jamiejcole/zenith/Code/MK2.5/test/interrupttest/interrupttest.ino

#include <Arduino.h>
#include <Wire.h>
#include "Adafruit_MCP23017.h"
#include "Rotary.h"
#include "RotaryEncOverMCP.h"

#define INTERRUPT_FUNC_ATTRIB IRAM_ATTR

/* Our I2C MCP23017 GPIO expanders */
Adafruit_MCP23017 mcp;

//Array of pointers of all MCPs if there is more than one
Adafruit_MCP23017* allMCPs[] = { &mcp };
constexpr int numMCPs = (int)(sizeof(allMCPs) / sizeof(*allMCPs));

/* the INT pin of the MCP can only be connected to
 * an interrupt capable pin on the Arduino, either
 * D3 or D2.
 * */
int arduinoIntPin = 12;

/* variable to indicate that an interrupt has occured */
volatile boolean awakenByInterrupt = false;

/* function prototypes */
void intCallBack();
void cleanInterrupts();
void handleInterrupt();
void RotaryEncoderChanged(bool clockwise, int id);

/* Array of all rotary encoders and their pins */
RotaryEncOverMCP rotaryEncoders[] = {
    // outputA,B on GPB7,GPB6, register with callback and ID=1 (GPB0=7 .. GPB7=15)
    RotaryEncOverMCP(&mcp, 6, 7, &RotaryEncoderChanged, 1),
    // outputA,B on GPA0,GPA1, register with callback and ID=2
    RotaryEncOverMCP(&mcp, 4, 5, &RotaryEncoderChanged, 2)
};
constexpr int numEncoders = (int)(sizeof(rotaryEncoders) / sizeof(*rotaryEncoders));

void RotaryEncoderChanged(bool clockwise, int id) {
    Serial.println("Encoder " + String(id) + ": "
            + (clockwise ? String("clockwise") : String("counter-clock-wise")));
}

void setup(){

    Serial.begin(115200);
    Serial.println("MCP23007 Interrupt Test");

    pinMode(arduinoIntPin,INPUT);

    mcp.begin();      // use default address 0
    Wire.setClock(400000);
    mcp.readINTCAPAB(); //read this so that the interrupt is cleared

    //initialize all rotary encoders

    //Setup interrupts, OR INTA, INTB together on both ports.
    //thus we will receive an interrupt if something happened on
    //port A or B with only a single INT connection.
    mcp.setupInterrupts(true,false,LOW);

    //Initialize input encoders (pin mode, interrupt)
    for(int i=0; i < numEncoders; i++) {
        rotaryEncoders[i].init();
    }

    attachInterrupt(digitalPinToInterrupt(arduinoIntPin), intCallBack, FALLING);
}

// The int handler will just signal that the int has happened
// we will do the work from the main loop.
void INTERRUPT_FUNC_ATTRIB intCallBack() {
    awakenByInterrupt=true;
}

void checkInterrupt() {
    if(awakenByInterrupt) {
        // disable interrupts while handling them.
        Serial.println("interrupt awoken! detaching interrupt...");
        detachInterrupt(digitalPinToInterrupt(arduinoIntPin));
        handleInterrupt();
        Serial.println("attaching interrupts!");
        mcp.readINTCAPAB();
        attachInterrupt(digitalPinToInterrupt(arduinoIntPin),intCallBack,FALLING);
    }
}

void handleInterrupt(){
    //Read the entire state when the interrupt occurred

    //An interrupt occurred on some MCP object.
    //since all of them are ORed together, we don't
    //know exactly which one has fired.
    //just read all of them, pre-emptively.
    Serial.println("handling interrupt!");
    for(int j = 0; j < numMCPs; j++) {
        uint16_t gpioAB = allMCPs[j]->readINTCAPAB();
        // we need to read GPIOAB to clear the interrupt actually.
        volatile uint16_t dummy = allMCPs[j]->readGPIOAB();
        for (int i=0; i < numEncoders; i++) {
            //only feed this in the encoder if this
            //is coming from the correct MCP
            if(rotaryEncoders[i].getMCP() == allMCPs[j])
                rotaryEncoders[i].feedInput(gpioAB);
                Serial.print("feeding encoder input ");
                Serial.println(i);
        }
    }

    cleanInterrupts();
}

// handy for interrupts triggered by buttons
// normally signal a few due to bouncing issues
void cleanInterrupts(){
#ifdef __AVR__
    EIFR=0x01;
#endif
    awakenByInterrupt=false;
    Serial.println("cleaning interrupts!");
}

void loop() {
    //Check if an interrupt has occurred and act on it
    checkInterrupt();
    delay(1);
}
