jamiejcole/zenith/Code/MK2.5/test/Bounce2mcp.h

/*
  The MIT License (MIT)

  Copyright (c) 2013 thomasfredericks

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
  THE SOFTWARE IS PROVIDED "AS IS", WITHOUT WARRANTY OF ANY KIND, EXPRESS OR
  IMPLIED, INCLUDING BUT NOT LIMITED TO THE WARRANTIES OF MERCHANTABILITY, FITNESS
  FOR A PARTICULAR PURPOSE AND NONINFRINGEMENT. IN NO EVENT SHALL THE AUTHORS OR
  COPYRIGHT HOLDERS BE LIABLE FOR ANY CLAIM, DAMAGES OR OTHER LIABILITY, WHETHER
  IN AN ACTION OF CONTRACT, TORT OR OTHERWISE, ARISING FROM, OUT OF OR IN
  CONNECTION WITH THE SOFTWARE OR THE USE OR OTHER DEALINGS IN THE SOFTWARE.
*/

/* * * * * * * * * * * * * * * * * * * * * * * * * * * *
  Main code by Thomas O Fredericks (tof@t-o-f.info)
  Previous contributions by Eric Lowry, Jim Schimpf and Tom Harkaway
  Modifications to add MCP23017 compatability made by Tenkai Kariya
  * * * * * * * * * * * * * * * * * * * * * * * * * * * * */

#ifdef BOUNCE_LOCK
#error You are using the invalid BOUNCE_LOCK-OUT define. Please update your sources to use BOUNCE_LOCK_OUT
#endif

// Uncomment the following line for "LOCK-OUT" debounce method
//#define BOUNCE_LOCK_OUT


#ifndef Bounce2mcp_h
#define Bounce2mcp_h

#include <inttypes.h>
#include "Adafruit_MCP23017.h"

class BounceMcp
{
 public:
    // Create an instance of the bounce library
    BounceMcp();

    // Attach to a MCP object, a pin (and also sets initial state), and set debounce interval.
    void attach(Adafruit_MCP23017 mcpX, int pin, uint16_t interval_millis);

    // Sets the debounce interval
    void interval(uint16_t interval_millis);

    // Updates the pin
    // Returns 1 if the state changed
    // Returns 0 if the state did not change
    bool update();

    // Returns the updated pin state
    bool read();

    // Returns the falling pin state
    bool fell();

    // Returns the rising pin state
    bool rose();

 protected:
    unsigned long previous_millis;
    uint16_t interval_millis;
    uint8_t state;
    uint8_t pin;
    Adafruit_MCP23017 mcpX;
};

#endif
