jamiejcole/zenith/Code/MK2.5/test/RotaryEncOverMCP.h

/*
 * RotaryEncOverMCP.h
 *
 *  Created on: 21.05.2018
 *      Author: Maxi
 */

#ifndef SRC_ROTARYENCOVERMCP_H_
#define SRC_ROTARYENCOVERMCP_H_

/* Describes new objects based on the Rotary and Adafruit MCP23017 library */
#include "Adafruit_MCP23017.h"
#include "Rotary.h"

/* function pointer definition */
typedef void (*rotaryActionFunc)(bool clockwise, int id);

/* We describe an object in which we instantiate a rotary encoder
 * over an I2C expander.
 * It holds the information:
 *  * to which MCP object it's connected
 *  * which pin it is connected to
 *  * what function to call when there is a change
 * */
class RotaryEncOverMCP {
public:
    RotaryEncOverMCP(Adafruit_MCP23017* mcp, byte pinA, byte pinB, rotaryActionFunc actionFunc = nullptr, int id = 0)
    : rot(pinA, pinB), mcp(mcp),
      pinA(pinA), pinB(pinB),
      actionFunc(actionFunc), id(id) {
    }

    /* Initialize object in the MCP */
    void init() {
        if(mcp != nullptr) {
            mcp->pinMode(pinA, INPUT);
            mcp->pullUp(pinA, 1); //disable pullup on this pin
            mcp->setupInterruptPin(pinA,CHANGE);
            mcp->pinMode(pinB, INPUT);
            mcp->pullUp(pinB, 1); //disable pullup on this pin
            mcp->setupInterruptPin(pinB,CHANGE);
        }
    }

    /* On an interrupt, can be called with the value of the GPIOAB register (or INTCAP) */
    void feedInput(uint16_t gpioAB) {
        uint8_t pinValA = bitRead(gpioAB, pinA);
        uint8_t pinValB = bitRead(gpioAB, pinB);
        uint8_t event = rot.process(pinValA, pinValB);
        if(event == DIR_CW || event == DIR_CCW) {
            //clock wise or counter-clock wise
            bool clockwise = event == DIR_CW;
            //Call into action function if registered
            if(actionFunc) {
                actionFunc(clockwise, id);
            }
        }
    }

    /* Poll the encoder. Will cause an I2C transfer. */
    void poll() {
        if(mcp != nullptr) {
            feedInput(mcp->readGPIOAB());
        }
    }

    Adafruit_MCP23017* getMCP() {
        return mcp;
    }

    int getID() {
        return id;
    }

private:
    Rotary rot;                         /* the rotary object which will be created*/
    Adafruit_MCP23017* mcp = nullptr;   /* pointer the I2C GPIO expander it's connected to */
    uint8_t pinA = 0;
    uint8_t pinB = 0;           /* the pin numbers for output A and output B */
    rotaryActionFunc actionFunc = nullptr;  /* function pointer, will be called when there is an action happening */
    int id = 0;                             /* optional ID for identification */
};


#endif /* SRC_ROTARYENCOVERMCP_H_ */
